jaromir-sukuba/pi_zero_computer/fw/keyboard/inc/main.h

/**
  ******************************************************************************
  * @file    USB_Device/HID_Standalone/Inc/main.h 
  * @author  MCD Application Team
  * @version V1.7.0
  * @date    04-November-2016
  * @brief   Header for main.c module
  ******************************************************************************
  * @attention
  *
  * <h2><center>&copy; Copyright (c) 2016 STMicroelectronics International N.V. 
  * All rights reserved.</center></h2>
  *
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
  ******************************************************************************
  */
  
/* Define to prevent recursive inclusion -------------------------------------*/
#ifndef __MAIN_H
#define __MAIN_H

/* Includes ------------------------------------------------------------------*/
#include "stm32f072b_discovery.h"
#include "usbd_core.h"
#include "usbd_desc.h"
#include "usbd_hid.h" 


/* Exported types ------------------------------------------------------------*/
/* Exported constants --------------------------------------------------------*/
/* Exported macro ------------------------------------------------------------*/

/* Uncomment the line below to select your USB clock source */
#define USE_USB_CLKSOURCE_CRSHSI48   1
//#define USE_USB_CLKSOURCE_PLL        1

#if !defined (USE_USB_CLKSOURCE_PLL) && !defined (USE_USB_CLKSOURCE_CRSHSI48)
 #error "Missing USB clock definition"
#endif
/* Exported functions ------------------------------------------------------- */
void Toggle_Leds(void);

#endif /* __MAIN_H */

/************************ (C) COPYRIGHT STMicroelectronics *****END OF FILE****/
